ManiacalLabs/WyoManiacalDisplay/Plastics/PanelConnector_1x2Long.stl

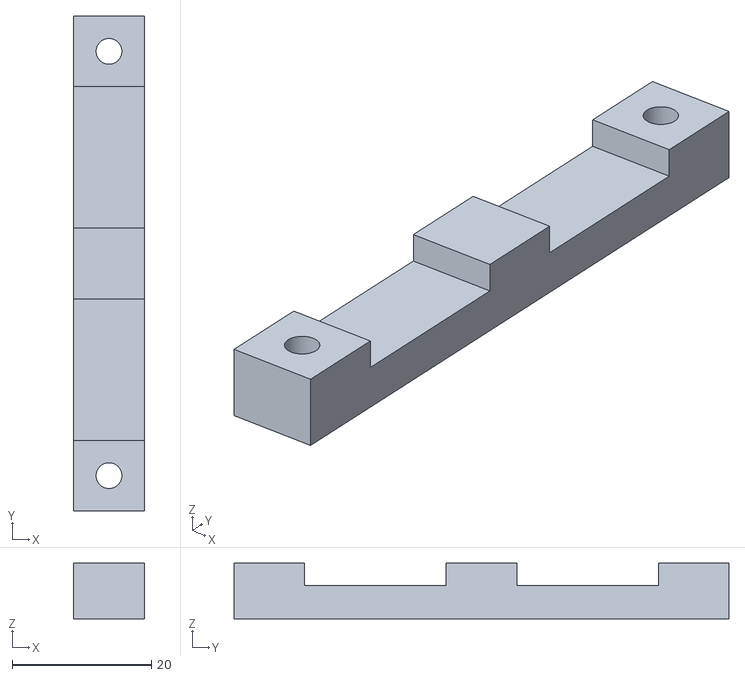
[picture p15: CAD file, 2016-03-05]
Plastics/PanelConnector_1x2Long.stl
10.2 x 71.1 x 8.00
