ManiacalLabs/WyoManiacalDisplay/Plastics/MetalRail_Nut.stl

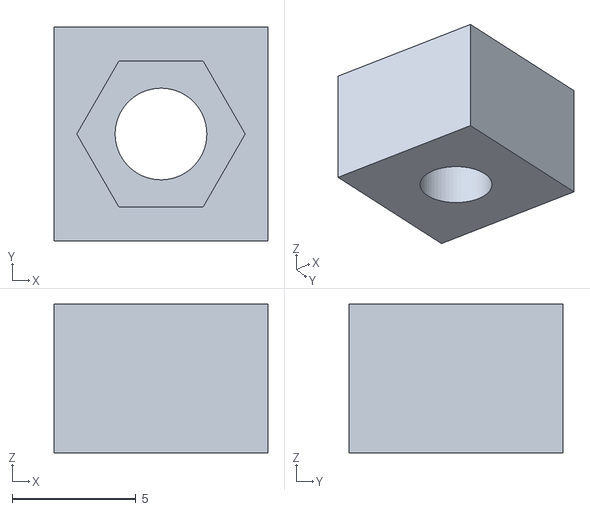
[picture p16: CAD file, 2016-03-05]
Plastics/MetalRail_Nut.stl
8.64 x 8.64 x 6.00
